ifilot/p2000t-sdcard/src/fat32.c

/**************************************************************************
 *                                                                        *
 *   Author: Ivo Filot <ivo@ivofilot.nl>                                  *
 *                                                                        *
 *   P2000T-SDCARD is free software:                                      *
 *   you can redistribute it and/or modify it under the terms of the      *
 *   GNU General Public License as published by the Free Software         *
 *   Foundation, either version 3 of the License, or (at your option)     *
 *   any later version.                                                   *
 *                                                                        *
 *   P2000T-SDCARD is distributed in the hope that it will be useful,     *
 *   but WITHOUT ANY WARRANTY; without even the implied warranty          *
 *   of MERCHANTABILITY or FITNESS FOR A PARTICULAR PURPOSE.              *
 *   See the GNU General Public License for more details.                 *
 *                                                                        *
 *   You should have received a copy of the GNU General Public License    *
 *   along with this program.  If not, see http://www.gnu.org/licenses/.  *
 *                                                                        *
 **************************************************************************/

#include "fat32.h"

uint16_t _bytes_per_sector = 0;
uint8_t _sectors_per_cluster = 0;
uint16_t _reserved_sectors = 0;
uint8_t _number_of_fats = 0;
uint32_t _sectors_per_fat = 0;
uint32_t _root_dir_first_cluster = 0;
uint32_t _linkedlist[16];
uint32_t _fat_begin_lba = 0;
uint32_t _SECTOR_begin_lba = 0;
uint32_t _lba_addr_root_dir = 0;
uint32_t _filesize_current_file = 0;
uint32_t _current_folder_cluster = 0;
uint8_t _filename[MAX_LFN_LENGTH+1];
char _ext[4] = {0};
char _base_name[9] = {0};
uint8_t _current_attrib = 0;

/**
 * @brief Read the Master Boot Record
 * 
 * @return uint32_t sector-address of the first partition
 */
uint32_t read_mbr(void) {
    // read the first sector of the SD card
    read_sector(0x00000000);

    if(ram_read_uint16_t(SDCACHE0 + 510) != 0xAA55) {
        return 0;
    } else {
        return ram_read_uint32_t(SDCACHE0 + 0x1C6);
    }
}

/**
 * @brief Read metadata of the partition
 * 
 * @param lba0 address of the partition
 */
void read_partition(uint32_t lba0) {
    // inform the reader that we are about to read partition 1
    print("Reading partition 1");

    // read the volume ID (first sector of the partition)
    read_sector(lba0);

    // collect data
    _bytes_per_sector = ram_read_uint16_t(SDCACHE0 + 0x0B);
    _sectors_per_cluster = ram_read_uint8_t(SDCACHE0 + 0x0D);
    _reserved_sectors = ram_read_uint16_t(SDCACHE0 + 0x0E);
    _number_of_fats = ram_read_uint8_t(SDCACHE0 + 0x10);
    _sectors_per_fat = ram_read_uint32_t(SDCACHE0 + 0x24);
    _root_dir_first_cluster = ram_read_uint32_t(SDCACHE0 + 0x2C);
    _current_folder_cluster = _root_dir_first_cluster;
    uint16_t signature = ram_read_uint16_t(SDCACHE0 + 0x1FE);

    // print data
    // sprintf(termbuffer, "LBA partition 1:%c%08lX", COL_GREEN, lba0);
    // terminal_printtermbuffer();

    // sprintf(termbuffer, "Bytes per sector:%c%i", COL_GREEN, _bytes_per_sector);
    // terminal_printtermbuffer();

    // sprintf(termbuffer, "Sectors per cluster:%c%i", COL_GREEN, _sectors_per_cluster);
    // terminal_printtermbuffer();

    // sprintf(termbuffer, "Reserved sectors:%c%i", COL_GREEN, _reserved_sectors);
    // terminal_printtermbuffer();

    // sprintf(termbuffer, "Number of FATS:%c%i", COL_GREEN, _number_of_fats);
    // terminal_printtermbuffer();

    // sprintf(termbuffer, "Sectors per FAT:%c%lu", COL_GREEN, _sectors_per_fat);
    // terminal_printtermbuffer();

    // calculate the total capacity on the partition; this corresponds to the
    // each FAT holds a number of sectors
    // each sector can refer to 128 clusters (128 x 32 = 512 bytes)
    // each cluster hosts a number of sectors
    // each sector has a specific sectors size (512 bytes for FAT32)
    sprintf(termbuffer, "Partition size:%c%lu MiB", COL_GREEN, (_sectors_per_fat * _sectors_per_cluster * _bytes_per_sector) >> 13 );
    terminal_printtermbuffer();

    // sprintf(termbuffer, "Root first cluster:%c%08lX", COL_GREEN, _root_dir_first_cluster);
    // terminal_printtermbuffer();

    // sprintf(termbuffer, "Signature:%c%04X", COL_GREEN, signature);
    // terminal_printtermbuffer();

    // consolidate variables
    _fat_begin_lba = lba0 + _reserved_sectors;
    _SECTOR_begin_lba = lba0 + _reserved_sectors + (_number_of_fats * _sectors_per_fat);
    _lba_addr_root_dir = calculate_sector_address(_root_dir_first_cluster, 0);

    // read first sector of first partition to establish volume name
    read_sector(_lba_addr_root_dir);

    // volume name is written as the first 11 bytes
    char volume_name[11];
    copy_from_ram(SDCACHE0, volume_name, 11);
    sprintf(termbuffer, "Volume name:%c%.11s", COL_GREEN, volume_name);
    terminal_printtermbuffer();
    memcpy(&vidmem[0x50+39-11], volume_name, 11);

    _flag_sdcard_mounted = 1;
}

/**
 * @brief Read the contents of the folder starting at address cluster and:
 *        - when file_id < 0, scan the directory and output the list of files
 *        - when file_id == 0, search for a file identified by basename_find and ext_find
 *        - when file_id > 0, search for a file identified by file id

 * @brief Find a file identified by BASENAME and EXT in the folder correspond
 *        to the cluster address
 * 
 * @param cluster        folder's first cluster address
 * @param file_id        ith file in the folder
 * @param casrun         whether we are performing a run with CAS file metadata scan
 * @param basename_find  first 8 bytes of the file to find
 * @param ext_find       3 byte extension of the file to find
 * @return uint32_t      cluster address of the file
 */
uint32_t read_folder_int(uint32_t cluster, int16_t file_id, uint8_t casrun, const char* basename_find, const char* ext_find) {

    // build linked list for the cluster addr
    build_linked_list(cluster);

    // loop over the clusters and read directory contents
    uint8_t ctr = 0;                // counter over clusters
    uint16_t fctr = 0;              // counter over directory entries (files and folders)
    uint32_t totalfilesize = 0;     // collect size of files in folder
    uint8_t stopreading = 0;        // whether to break of reading procedure
    uint8_t firstPos = 0;
    uint8_t lfn_found = 0; 

    while(_linkedlist[ctr] != 0xFFFFFFFF && ctr < F_LL_SIZE && stopreading == 0) {
        
        // print cluster number and address
        uint32_t caddr = calculate_sector_address(_linkedlist[ctr], 0);

        // loop over all sectors per cluster
        for(uint8_t i=0; i<_sectors_per_cluster && stopreading == 0; i++) {
            read_sector(caddr++);            // read next sector data
            for(uint16_t loc=SDCACHE0; loc<SDCACHE0+16*32; loc+=32) { // 16 file tables per sector
                // check first position
                firstPos = ram_read_uint8_t(loc);
                _current_attrib = ram_read_uint8_t(loc + 0x0B);    // attrib byte

                // continue if an unused entry is encountered 0xE5
                if(firstPos == 0xE5) {
                    continue;
                }

                // early exit if a zero is read
                if(firstPos == 0x00) {
                    stopreading = 1;
                    break;
                }

                // check for LFN entry
                if ((_current_attrib & 0x0F) == 0x0F) {
                    if (file_id < 0 || file_id == fctr+1) {
                        if (!lfn_found) {
                            lfn_found = 1;  // indicate LNF found
                            memset(_filename, 0, MAX_LFN_LENGTH+1);
                        }
                        uint8_t seq = firstPos & 0x1F;  // LFN sequence number
                        uint8_t k = 0;
                        if (seq <= 2) {
                            // extract characters from LFN entry
                            for (k = 0; k < 5; k++) _filename[(seq - 1) * 13 + k] = ram_read_uint8_t(loc + 1 + k * 2);
                            for (k = 0; k < 6; k++) _filename[(seq - 1) * 13 + 5 + k] = ram_read_uint8_t(loc + 14 + k * 2);
                            for (k = 0; k < 2; k++) _filename[(seq - 1) * 13 + 11 + k] = ram_read_uint8_t(loc + 28 + k * 2);
                        }
                        continue;
                    }
                }

                // check for non-hidden, non-system, non-volumeID SFN entry
                if((_current_attrib & 0b00001110) == 0) {
                    if(firstPos != '.' || ram_read_uint8_t(loc+1) == '.') { // skip dotfiles but keep ".." parent folder
                        // capture metadata
                        fctr++;
                        if (file_id < 0 || fctr == file_id || file_id == 0) {
                            const uint32_t fc = grab_cluster_address_from_fileblock(loc);
                            _filesize_current_file = ram_read_uint32_t(loc + 0x1C);
                            totalfilesize += _filesize_current_file;
                            
                            // copy DOS base name and extension
                            copy_from_ram(loc, _base_name, 8);
                            copy_from_ram(loc+0x08, _ext, 3);

                            if (file_id == 0) {
                                if (memcmp(basename_find, _base_name, 8) == 0 && memcmp(ext_find, _ext, 3) == 0) {
                                    return fc;
                                } else {
                                    continue;
                                }
                            }

                            // if no LFN found, the SFN filename needs to be formatted
                            if (!lfn_found) {
                                memcpy(_filename, _base_name, 8); // copy base name
                                memcpy(&_filename[9], _ext, 4); // copy extension (incl terminator)
                                // if file, inject dot before extension
                                _filename[8] = (_current_attrib & 0x10) ? '\0' : '.';
                                // remove superfluous spaces before extension
                                uint8_t k = 0;
                                for (k = 7; k >= 1 && _filename[k] == ' '; k--);
                                if (k < 7) memcpy(&_filename[k+1], &_filename[8], 5);
                            }

                            if(file_id < 0) {
                                if(_current_attrib & 0x10) { // directory entry
                                    sprintf(termbuffer, "%c%3u%c%-24.24s%c (dir)", COL_YELLOW, fctr, COL_WHITE, _filename, COL_CYAN);
                                } else {             // file entry
                                    if(casrun == 1 && memcmp(_ext, "CAS", 3) == 0) {    // cas file
                                        // read from SD card once more and extract CAS data
                                        read_sector_to(calculate_sector_address(fc, 0), SDCACHE1);

                                        // grab CAS metadata
                                        uint8_t casname[16];
                                        uint8_t ext[3];
                                        copy_from_ram(SDCACHE1 + 0x36, casname, 8);
                                        copy_from_ram(SDCACHE1 + 0x47, &casname[8], 8);
                                        copy_from_ram(SDCACHE1 + 0x3E, ext, 3);

                                        // replace terminating characters (0x00) by spaces (0x20)
                                        replace_bytes(casname, 0x00, 0x20, 16);
                                        replace_bytes(ext, 0x00, 0x20, 3);

                                        const uint16_t filesize = ram_read_uint16_t(SDCACHE1 + 0x32);
                                        const uint8_t blocks = ram_read_uint8_t(SDCACHE1 + 0x4F);
                                        sprintf(termbuffer, "%c%3u%c%.16s %.3s%c%2i  %6u", COL_GREEN, fctr, COL_YELLOW, casname, ext, COL_CYAN, blocks, filesize);
                                    } else { // non-cas file or not a cas run
                                        sprintf(termbuffer, "%c%3u%c%-24.24s%c%6lu", COL_GREEN, fctr, COL_WHITE, _filename, COL_YELLOW, _filesize_current_file);
                                    }
                                }
                                terminal_printtermbuffer();

                                if(fctr % 16 == 0) {
                                    print_recall("-- Press key to continue, q to quit --");
                                    if(wait_for_key_fixed(3) == 1) {
                                        stopreading = 1;
                                        break;
                                    }
                                }
                            }

                            if(fctr == file_id) {
                                return fc;
                            }
                        }
                    }
                }
                lfn_found = 0; // reset LFN tracking 
            }
        }
        ctr++;  // next cluster
    }

    if (file_id == 0) return 0; // if file_id is 0, we return 0 to indicate no file found

    if(file_id < 0) {
        sprintf(termbuffer, "%6u File(s) %10lu Bytes", fctr, totalfilesize);
        terminal_printtermbuffer();
    }

    return _root_dir_first_cluster;
}

/**
 * @brief Read the contents of the root folder and search for a file identified 
 *        by file id. When a negative file_id is supplied, the directory is
 *        simply scanned and the list of files are outputted to the screen.
 * 
 * @param file_id ith file in the folder
 * @return uint32_t first cluster of the file or directory
 */
uint32_t read_folder(int16_t file_id, uint8_t casrun) {
    return read_folder_int(_current_folder_cluster, file_id, casrun, NULL, NULL);
}

/**
 * @brief Find a file identified by BASENAME and EXT in the folder correspond
 *        to the cluster address
 * 
 * @param cluster   cluster address
 * @param basename  first 8 bytes of the file
 * @param ext       3 byte extension of the file
 * @return uint32_t cluster address of the file or 0 if not found
 */
uint32_t find_file(uint32_t cluster, const char* basename_find, const char* ext_find) {
    return read_folder_int(cluster, 0, 0, basename_find, ext_find);
}

/**
 * @brief Build a linked list of sector addresses starting from a root address
 * 
 * @param nextcluster first cluster in the linked list
 */
void build_linked_list(uint32_t nextcluster) {
    // counter over clusters
    uint8_t ctr = 0;

    // clear previous linked list
    memset(_linkedlist, 0xFF, F_LL_SIZE * sizeof(uint32_t));

    // try grabbing next cluster
    while(nextcluster < 0x0FFFFFF8 && nextcluster != 0 && ctr < F_LL_SIZE) {
        _linkedlist[ctr] = nextcluster;
        read_sector(_fat_begin_lba + (nextcluster >> 7));
        uint8_t item = nextcluster & 0b01111111;
        nextcluster = ram_read_uint32_t(item * 4);
        ctr++;
    }
}

/**
 * @brief Calculate the sector address from cluster and sector
 * 
 * @param cluster which cluster
 * @param sector which sector on the cluster (0-Nclusters)
 * @return uint32_t sector address (512 byte address)
 */
uint32_t calculate_sector_address(uint32_t cluster, uint8_t sector) {
    return _SECTOR_begin_lba + (cluster - 2) * _sectors_per_cluster + sector;   
}

/**
 * @brief Construct sector address from file entry
 * 
 * @return uint32_t 
 */
uint32_t grab_cluster_address_from_fileblock(uint16_t loc) {
    return (uint32_t)ram_read_uint16_t(loc + 0x14) << 16 | 
                     ram_read_uint16_t(loc + 0x1A);
}

/**
 * @brief Store a file in the external ram
 * 
 * @param faddr    cluster address of the file
 * @param ram_addr first position in ram to store the file
 * @param verbose  whether to show progress
 */
void store_cas_ram(uint32_t faddr, uint16_t ram_addr) {
    build_linked_list(faddr);

    // count number of clusters
    uint8_t ctr = 0;
    uint8_t total_sectors = (_filesize_current_file + 511) / 512;
    uint32_t caddr = 0;
    uint16_t nbytes = 0;    // count number of bytes
    uint8_t sector_ctr = 0; // counter sector
    uint8_t first_sector = 1; // whether this is the first sector

    ctr = 0;
    while(_linkedlist[ctr] != 0xFFFFFFFF && ctr < 16 && nbytes < _filesize_current_file) {

        // calculate address of sector
        caddr = calculate_sector_address(_linkedlist[ctr], 0);

        // loop over all sectors given a cluster and copy the data to RAM
        for(uint8_t i=0; i<_sectors_per_cluster; i++) {

            read_sector_to(caddr + i, ram_addr); // read sector data (512 bytes) to external ram address
            switch(sector_ctr % 5) {
            case 0:
                // preamble is first 0x100 bytes of sector
                if (first_sector) {
                    // first sector, copy the preamble's transfer address and length
                    ram_write_uint16_t(0x8000, ram_read_uint16_t(SDCACHE0 + 0x0030));
                    ram_write_uint16_t(0x8002, ram_read_uint16_t(SDCACHE0 + 0x0032));
                    first_sector = 0;
                }
                ram_transfer(ram_addr + 0x100, ram_addr, 0x100);
                ram_addr += 256;
                break;
            case 2:
                // preamble is last 0x100 bytes of sector
                ram_addr += 256;
                break;
            default: // 1,3,4 are complete blocks
                ram_addr += 512;
                break;
            }

            sprintf(termbuffer, "Loading %i / %i sectors", sector_ctr, total_sectors);
            terminal_redoline();

            nbytes += 512;
            if(nbytes >= _filesize_current_file) {
                break;
            }
            sector_ctr++;
        }

        ctr++;
    }

    sprintf(termbuffer, "Done loading %i / %i sectors", 
                total_sectors, total_sectors);
    terminal_printtermbuffer();
}

/**
 * @brief Store a file in the internal ram
 * 
 * @param faddr    cluster address of the file
 * @param ram_addr first position in ram to store the file
 */
void store_prg_intram(uint32_t faddr, uint16_t ram_addr) {
    build_linked_list(faddr);

    // count number of clusters
    uint8_t ctr = 0;
    uint8_t cursec = 0;
    uint8_t total_sectors = (_filesize_current_file + 511) / 512;
    uint32_t caddr = 0;
    uint16_t nbytes = 0;    // count number of bytes

    ctr = 0;
    while(_linkedlist[ctr] != 0xFFFFFFFF && ctr < 16 && nbytes < _filesize_current_file) {

        // calculate address of sector
        caddr = calculate_sector_address(_linkedlist[ctr], 0);

        sprintf(termbuffer, "Copying program to %04X", ram_addr);
        terminal_printtermbuffer();

        // loop over all sectors given a cluster and copy the data to RAM
        for(uint8_t i=0; i<_sectors_per_cluster; i++) {

            // copy sector over to internal memory
            open_command();
            cmd17(caddr);
            fast_sd_to_intram_full(ram_addr);
            close_command();

            // increment ram pointer
            ram_addr += 0x200;

            sprintf(termbuffer, "Loading %i / %i sectors", cursec, total_sectors);
            terminal_redoline();

            nbytes += 512;
            if(nbytes >= _filesize_current_file) {
                break;
            }
            caddr++;
            cursec++;
        }

        ctr++;
    }

    sprintf(termbuffer, "Done loading %i / %i sectors", 
                total_sectors, total_sectors);
    terminal_printtermbuffer();
}
